ElwinBoots/Teensy_DualMotorBoard_V1/Firmware/MotionProfile.h

#ifndef __MOTIONPROFILE2_H__
#define __MOTIONPROFILE2_H__

class MotionProfile{		
public:	
	MotionProfile(float tstart, float t1, float t2, float t3, float p, float v_max, float a_max, float j_max, float Ts);	 
	void init();
	double stateCalculation( int input_status);
	double p2p_get_b( double t );
	double qref, vref, aref, jref;

	long REFstatus; 
	bool REFidir;
	float v, v_max, a_max, j_max, tstart, t1, t2, t3, Ts, rdelay;
	double REFiref, REFqmem;
  double p;
	double t, REFt0, REFt1, REFt2, REFt3, REFt4, REFt5, REFt6, REFt7, reltim;
	double REFs0, REFs1, REFs2, REFs3, REFs4, REFs5, REFs6, REFs7;
	double REFv0, REFv1, REFv2, REFv3, REFv4, REFv5, REFv6, REFv7;
	double REFa0, REFa1, REFa2, REFa3, REFa4, REFa5, REFa6, REFa7;
	double REFdelta, REFgamma, REFjerk, REFxstrt, j, jd;
	
protected:

	
	

};
#endif
