ElwinBoots/Teensy_DualMotorBoard_V1/trace.h

enum type {
  TYPE_INT8,
  TYPE_UINT8,
  TYPE_INT16,
  TYPE_UINT16,
  TYPE_INT32,
  TYPE_UINT32,
  TYPE_INT64,
  TYPE_UINT64,
  TYPE_FLOAT32,
  TYPE_FLOAT64
};

typedef struct trace_t{ 
  const char* names[500]; 
  uint8_t  all_types[500]; 
  uint8_t* all_pointers[500]; 
  uint32_t  all_lengths[500]; 
  uint8_t*  pointers[50]; 
  uint32_t  lengths[50]; 
  uint32_t n_to_send;
  bool send_all;
} trace_t; 

trace_t trace = 
{ 
  {
	"motor.conf1.anglechoice",
	"motor.conf1.advancefactor",
	"motor.conf1.reversecommutation",
	"motor.conf1.maxDutyCycle",
	"motor.conf1.ridethewave",
	"motor.conf1.commutationoffset",
	"motor.conf1.adc2A",
	"motor.conf1.ss_gain",
	"motor.conf1.enccountperrev",
	"motor.conf1.enc2rad",
	"motor.conf1.I_max",
	"motor.conf1.T_max",
	"motor.conf1.Kp_iq",
	"motor.conf1.Kp_id",
	"motor.conf1.Ki_iq",
	"motor.conf1.Ki_id",
	"motor.conf1.lowpass_Vq_c",
	"motor.conf1.lowpass_Vd_c",
	"motor.conf1.max_edeltarad",
	"motor.conf1.N_pp",
	"motor.conf1.clipMethod",
	"motor.conf1.maxerror",
	"motor.conf1.Command",
	"motor.conf1.Ld",
	"motor.conf1.Lq",
	"motor.conf1.Lambda_m",
	"motor.conf1.Kp",
	"motor.conf1.Ki",
	"motor.conf1.Kd",
	"motor.conf1.lowpass_c",
	"motor.conf1.Kp_prep",
	"motor.conf1.Ki_prep",
	"motor.conf1.Kd_prep",
	"motor.conf1.lowpass_c_prep",
	"motor.conf1.enc_transmission",
	"motor.conf2.anglechoice",
	"motor.conf2.advancefactor",
	"motor.conf2.reversecommutation",
	"motor.conf2.maxDutyCycle",
	"motor.conf2.ridethewave",
	"motor.conf2.commutationoffset",
	"motor.conf2.adc2A",
	"motor.conf2.ss_gain",
	"motor.conf2.enccountperrev",
	"motor.conf2.enc2rad",
	"motor.conf2.I_max",
	"motor.conf2.T_max",
	"motor.conf2.Kp_iq",
	"motor.conf2.Kp_id",
	"motor.conf2.Ki_iq",
	"motor.conf2.Ki_id",
	"motor.conf2.lowpass_Vq_c",
	"motor.conf2.lowpass_Vd_c",
	"motor.conf2.max_edeltarad",
	"motor.conf2.N_pp",
	"motor.conf2.clipMethod",
	"motor.conf2.maxerror",
	"motor.conf2.Command",
	"motor.conf2.Ld",
	"motor.conf2.Lq",
	"motor.conf2.Lambda_m",
	"motor.conf2.Kp",
	"motor.conf2.Ki",
	"motor.conf2.Kd",
	"motor.conf2.lowpass_c",
	"motor.conf2.Kp_prep",
	"motor.conf2.Ki_prep",
	"motor.conf2.Kd_prep",
	"motor.conf2.lowpass_c_prep",
	"motor.conf2.enc_transmission",
	"motor.conf.Ts",
	"motor.conf.T",
	"motor.conf.Busadc2Vbus",
	"motor.conf.V_Bus",
	"motor.conf.Ndownsample",
	"motor.conf.NdownsamplePRBS",
	"motor.conf.ss_fstart",
	"motor.conf.ss_fstep",
	"motor.conf.ss_fend",
	"motor.conf.ss_n_aver",
	"motor.state.sens1",
	"motor.state.sens2",
	"motor.state.sens3",
	"motor.state.sens4",
	"motor.state.sens1_lp",
	"motor.state.sens2_lp",
	"motor.state.sens3_lp",
	"motor.state.sens4_lp",
	"motor.state.sens1_calib",
	"motor.state.sens2_calib",
	"motor.state.sens3_calib",
	"motor.state.sens4_calib",
	"motor.state.sensBus_lp",
	"motor.state.sensCalVal1",
	"motor.state.sensCalVal2",
	"motor.state.sensCalVal3",
	"motor.state.sensCalVal4",
	"motor.state.sensBus",
	"motor.state.sensBus2",
	"motor.state.n_senscalib",
	"motor.state.setupready",
	"motor.state.curtime",
	"motor.state.prevtime",
	"motor.state.overloadcounter",
	"motor.state.is_v7",
	"motor.state.firsterror",
	"motor.state.curloop",
	"motor.state.downsample",
	"motor.state.ss_phase",
	"motor.state.lfsr",
	"motor.state.noisebit",
	"motor.state.ss_f",
	"motor.state.ss_tstart",
	"motor.state.downsamplePRBS",
	"motor.state.encoderPos1",
	"motor.state.encoderPos2",
	"motor.state.IndexFound1",
	"motor.state.IndexFound2",
	"motor.state1.streambuffer",
	"motor.state1.curbuffer",
	"motor.state1.buffergain",
	"motor.state1.runstream",
	"motor.state1.T_FF_acc",
	"motor.state1.T_FF_vel",
	"motor.state1.i_vector_radpers_act",
	"motor.state1.BEMFa",
	"motor.state1.BEMFb",
	"motor.state1.Ialpha_prev",
	"motor.state1.Ibeta_prev",
	"motor.state1.Vq",
	"motor.state1.Vd",
	"motor.state1.Valpha",
	"motor.state1.Vbeta",
	"motor.state1.thetawave",
	"motor.state1.Id_meas",
	"motor.state1.Iq_meas",
	"motor.state1.Id_meas_lp",
	"motor.state1.Iq_meas_lp",
	"motor.state1.Va",
	"motor.state1.Vb",
	"motor.state1.Vc",
	"motor.state1.VSP",
	"motor.state1.i_vector_radpers",
	"motor.state1.i_vector_acc",
	"motor.state1.Kp_out",
	"motor.state1.Kp_out_prev",
	"motor.state1.Kd_out",
	"motor.state1.Ki_sum",
	"motor.state1.Ki_out",
	"motor.state1.lp_out",
	"motor.state1.biquadout",
	"motor.state1.mechcontout",
	"motor.state1.Iout",
	"motor.state1.muziek_gain",
	"motor.state1.muziek_gain_V",
	"motor.state1.downsample",
	"motor.state1.REFstatus",
	"motor.state1.incomingByte",
	"motor.state1.encoderPos1",
	"motor.state1.encoderPos2",
	"motor.state1.IndexFound1",
	"motor.state1.IndexFound2",
	"motor.state1.OutputOn",
	"motor.state1.ss_out",
	"motor.state1.distoff",
	"motor.state1.dist",
	"motor.state1.distval",
	"motor.state1.SP_input_status",
	"motor.state1.spGO",
	"motor.state1.Jload",
	"motor.state1.velFF",
	"motor.state1.R",
	"motor.state1.offsetVelTot",
	"motor.state1.offsetVel",
	"motor.state1.offsetVel_lp",
	"motor.state1.offsetVel_lp_prev",
	"motor.state1.jerk",
	"motor.state1.acc",
	"motor.state1.vel",
	"motor.state1.Ialpha",
	"motor.state1.Ibeta",
	"motor.state1.thetaPark",
	"motor.state1.thetaParkPrev",
	"motor.state1.edeltarad",
	"motor.state1.eradpers_lp",
	"motor.state1.erpm",
	"motor.state1.thetaPark_enc",
	"motor.state1.thetaPark_obs",
	"motor.state1.thetaPark_obs_prev",
	"motor.state1.co",
	"motor.state1.si",
	"motor.state1.tA",
	"motor.state1.tB",
	"motor.state1.tC",
	"motor.state1.Id_e",
	"motor.state1.Id_SP",
	"motor.state1.Iq_e",
	"motor.state1.Iq_SP",
	"motor.state1.ia",
	"motor.state1.ib",
	"motor.state1.ic",
	"motor.state1.Vq_distgain",
	"motor.state1.Vd_distgain",
	"motor.state1.Iq_distgain",
	"motor.state1.Id_distgain",
	"motor.state1.mechdistgain",
	"motor.state1.rdistgain",
	"motor.state1.maxVolt",
	"motor.state1.Vtot",
	"motor.state1.rmech",
	"motor.state1.rdelay",
	"motor.state1.emech",
	"motor.state1.ymech",
	"motor.state1.rmechoffset",
	"motor.state1.we",
	"motor.state1.VqFF",
	"motor.state1.VdFF",
	"motor.state1.Iq_offset_SP",
	"motor.state1.Id_offset_SP",
	"motor.state1.Valpha_offset",
	"motor.state1.Vbeta_offset",
	"motor.state1.vq_int_state",
	"motor.state1.vd_int_state",
	"motor.state1.I_bus",
	"motor.state1.P_tot",
	"motor.state1.Kp_iq_out",
	"motor.state1.Ki_iq_out",
	"motor.state1.Kp_id_out",
	"motor.state1.Ki_id_out",
	"motor.state1.Vq_lp_out",
	"motor.state1.Vd_lp_out",
	"motor.state1.Vq_biquadout",
	"motor.state1.Vd_biquadout",
	"motor.state1.SPdir",
	"motor.state1.spNgo",
	"motor.state1.hfi_on",
	"motor.state1.hfi_V",
	"motor.state1.hfi_V_act",
	"motor.state1.hfi_dir",
	"motor.state1.hfi_dir_int",
	"motor.state1.hfi_gain",
	"motor.state1.hfi_curangleest",
	"motor.state1.hfi_gain_int2",
	"motor.state1.hfi_Id_meas_low",
	"motor.state1.hfi_Iq_meas_low",
	"motor.state1.hfi_Id_meas_high",
	"motor.state1.hfi_Iq_meas_high",
	"motor.state1.delta_id",
	"motor.state1.delta_iq",
	"motor.state1.hfi_firstcycle",
	"motor.state1.hfi_abs_pos",
	"motor.state1.hfi_useforfeedback",
	"motor.state1.hfi_use_lowpass",
	"motor.state1.hfi_prev",
	"motor.state1.hfi_distgain",
	"motor.state1.hfi_contout",
	"motor.state1.hfi_error",
	"motor.state1.hfi_method",
	"motor.state1.hfi_ffw",
	"motor.state1.hfi_maxvel",
	"motor.state1.diq_compensation",
	"motor.state1.diq_compensation_on",
	"motor.state1.compensation",
	"motor.state1.firsterror",
	"motor.state2.streambuffer",
	"motor.state2.curbuffer",
	"motor.state2.buffergain",
	"motor.state2.runstream",
	"motor.state2.T_FF_acc",
	"motor.state2.T_FF_vel",
	"motor.state2.i_vector_radpers_act",
	"motor.state2.BEMFa",
	"motor.state2.BEMFb",
	"motor.state2.Ialpha_prev",
	"motor.state2.Ibeta_prev",
	"motor.state2.Vq",
	"motor.state2.Vd",
	"motor.state2.Valpha",
	"motor.state2.Vbeta",
	"motor.state2.thetawave",
	"motor.state2.Id_meas",
	"motor.state2.Iq_meas",
	"motor.state2.Id_meas_lp",
	"motor.state2.Iq_meas_lp",
	"motor.state2.Va",
	"motor.state2.Vb",
	"motor.state2.Vc",
	"motor.state2.VSP",
	"motor.state2.i_vector_radpers",
	"motor.state2.i_vector_acc",
	"motor.state2.Kp_out",
	"motor.state2.Kp_out_prev",
	"motor.state2.Kd_out",
	"motor.state2.Ki_sum",
	"motor.state2.Ki_out",
	"motor.state2.lp_out",
	"motor.state2.biquadout",
	"motor.state2.mechcontout",
	"motor.state2.Iout",
	"motor.state2.muziek_gain",
	"motor.state2.muziek_gain_V",
	"motor.state2.downsample",
	"motor.state2.REFstatus",
	"motor.state2.incomingByte",
	"motor.state2.encoderPos1",
	"motor.state2.encoderPos2",
	"motor.state2.IndexFound1",
	"motor.state2.IndexFound2",
	"motor.state2.OutputOn",
	"motor.state2.ss_out",
	"motor.state2.distoff",
	"motor.state2.dist",
	"motor.state2.distval",
	"motor.state2.SP_input_status",
	"motor.state2.spGO",
	"motor.state2.Jload",
	"motor.state2.velFF",
	"motor.state2.R",
	"motor.state2.offsetVelTot",
	"motor.state2.offsetVel",
	"motor.state2.offsetVel_lp",
	"motor.state2.offsetVel_lp_prev",
	"motor.state2.jerk",
	"motor.state2.acc",
	"motor.state2.vel",
	"motor.state2.Ialpha",
	"motor.state2.Ibeta",
	"motor.state2.thetaPark",
	"motor.state2.thetaParkPrev",
	"motor.state2.edeltarad",
	"motor.state2.eradpers_lp",
	"motor.state2.erpm",
	"motor.state2.thetaPark_enc",
	"motor.state2.thetaPark_obs",
	"motor.state2.thetaPark_obs_prev",
	"motor.state2.co",
	"motor.state2.si",
	"motor.state2.tA",
	"motor.state2.tB",
	"motor.state2.tC",
	"motor.state2.Id_e",
	"motor.state2.Id_SP",
	"motor.state2.Iq_e",
	"motor.state2.Iq_SP",
	"motor.state2.ia",
	"motor.state2.ib",
	"motor.state2.ic",
	"motor.state2.Vq_distgain",
	"motor.state2.Vd_distgain",
	"motor.state2.Iq_distgain",
	"motor.state2.Id_distgain",
	"motor.state2.mechdistgain",
	"motor.state2.rdistgain",
	"motor.state2.maxVolt",
	"motor.state2.Vtot",
	"motor.state2.rmech",
	"motor.state2.rdelay",
	"motor.state2.emech",
	"motor.state2.ymech",
	"motor.state2.rmechoffset",
	"motor.state2.we",
	"motor.state2.VqFF",
	"motor.state2.VdFF",
	"motor.state2.Iq_offset_SP",
	"motor.state2.Id_offset_SP",
	"motor.state2.Valpha_offset",
	"motor.state2.Vbeta_offset",
	"motor.state2.vq_int_state",
	"motor.state2.vd_int_state",
	"motor.state2.I_bus",
	"motor.state2.P_tot",
	"motor.state2.Kp_iq_out",
	"motor.state2.Ki_iq_out",
	"motor.state2.Kp_id_out",
	"motor.state2.Ki_id_out",
	"motor.state2.Vq_lp_out",
	"motor.state2.Vd_lp_out",
	"motor.state2.Vq_biquadout",
	"motor.state2.Vd_biquadout",
	"motor.state2.SPdir",
	"motor.state2.spNgo",
	"motor.state2.hfi_on",
	"motor.state2.hfi_V",
	"motor.state2.hfi_V_act",
	"motor.state2.hfi_dir",
	"motor.state2.hfi_dir_int",
	"motor.state2.hfi_gain",
	"motor.state2.hfi_curangleest",
	"motor.state2.hfi_gain_int2",
	"motor.state2.hfi_Id_meas_low",
	"motor.state2.hfi_Iq_meas_low",
	"motor.state2.hfi_Id_meas_high",
	"motor.state2.hfi_Iq_meas_high",
	"motor.state2.delta_id",
	"motor.state2.delta_iq",
	"motor.state2.hfi_firstcycle",
	"motor.state2.hfi_abs_pos",
	"motor.state2.hfi_useforfeedback",
	"motor.state2.hfi_use_lowpass",
	"motor.state2.hfi_prev",
	"motor.state2.hfi_distgain",
	"motor.state2.hfi_contout",
	"motor.state2.hfi_error",
	"motor.state2.hfi_method",
	"motor.state2.hfi_ffw",
	"motor.state2.hfi_maxvel",
	"motor.state2.diq_compensation",
	"motor.state2.diq_compensation_on",
	"motor.state2.compensation",
	"motor.state2.firsterror",
  }
,
  {
	 TYPE_INT32,
	 TYPE_FLOAT32,
	 TYPE_INT8,
	 TYPE_FLOAT32,
	 TYPE_UINT32,
	 TYPE_FLOAT32,
	 TYPE_FLOAT32,
	 TYPE_FLOAT32,
	 TYPE_INT32,
	 TYPE_FLOAT64,
	 TYPE_FLOAT32,
	 TYPE_FLOAT32,
	 TYPE_FLOAT32,
	 TYPE_FLOAT32,
	 TYPE_FLOAT32,
	 TYPE_FLOAT32,
	 TYPE_FLOAT32,
	 TYPE_FLOAT32,
	 TYPE_FLOAT32,
	 TYPE_FLOAT32,
	 TYPE_UINT32,
	 TYPE_FLOAT32,
	 TYPE_UINT32,
	 TYPE_FLOAT32,
	 TYPE_FLOAT32,
	 TYPE_FLOAT32,
	 TYPE_FLOAT32,
	 TYPE_FLOAT32,
	 TYPE_FLOAT32,
	 TYPE_FLOAT32,
	 TYPE_FLOAT32,
	 TYPE_FLOAT32,
	 TYPE_FLOAT32,
	 TYPE_FLOAT32,
	 TYPE_FLOAT32,
	 TYPE_INT32,
	 TYPE_FLOAT32,
	 TYPE_INT8,
	 TYPE_FLOAT32,
	 TYPE_UINT32,
	 TYPE_FLOAT32,
	 TYPE_FLOAT32,
	 TYPE_FLOAT32,
	 TYPE_INT32,
	 TYPE_FLOAT64,
	 TYPE_FLOAT32,
	 TYPE_FLOAT32,
	 TYPE_FLOAT32,
	 TYPE_FLOAT32,
	 TYPE_FLOAT32,
	 TYPE_FLOAT32,
	 TYPE_FLOAT32,
	 TYPE_FLOAT32,
	 TYPE_FLOAT32,
	 TYPE_FLOAT32,
	 TYPE_UINT32,
	 TYPE_FLOAT32,
	 TYPE_UINT32,
	 TYPE_FLOAT32,
	 TYPE_FLOAT32,
	 TYPE_FLOAT32,
	 TYPE_FLOAT32,
	 TYPE_FLOAT32,
	 TYPE_FLOAT32,
	 TYPE_FLOAT32,
	 TYPE_FLOAT32,
	 TYPE_FLOAT32,
	 TYPE_FLOAT32,
	 TYPE_FLOAT32,
	 TYPE_FLOAT32,
	 TYPE_FLOAT32,
	 TYPE_FLOAT32,
	 TYPE_FLOAT32,
	 TYPE_FLOAT32,
	 TYPE_UINT32,
	 TYPE_UINT32,
	 TYPE_FLOAT32,
	 TYPE_FLOAT32,
	 TYPE_FLOAT32,
	 TYPE_UINT32,
	 TYPE_FLOAT32,
	 TYPE_FLOAT32,
	 TYPE_FLOAT32,
	 TYPE_FLOAT32,
	 TYPE_FLOAT32,
	 TYPE_FLOAT32,
	 TYPE_FLOAT32,
	 TYPE_FLOAT32,
	 TYPE_FLOAT32,
	 TYPE_FLOAT32,
	 TYPE_FLOAT32,
	 TYPE_FLOAT32,
	 TYPE_FLOAT32,
	 TYPE_FLOAT32,
	 TYPE_FLOAT32,
	 TYPE_FLOAT32,
	 TYPE_FLOAT32,
	 TYPE_FLOAT32,
	 TYPE_FLOAT32,
	 TYPE_INT32,
	 TYPE_INT8,
	 TYPE_UINT32,
	 TYPE_UINT32,
	 TYPE_UINT32,
	 TYPE_INT8,
	 TYPE_UINT32,
	 TYPE_UINT32,
	 TYPE_UINT32,
	 TYPE_FLOAT32,
	 TYPE_UINT16,
	 TYPE_UINT16,
	 TYPE_FLOAT32,
	 TYPE_FLOAT32,
	 TYPE_UINT32,
	 TYPE_INT32,
	 TYPE_INT32,
	 TYPE_UINT32,
	 TYPE_UINT32,
	 TYPE_FLOAT32,
	 TYPE_UINT32,
	 TYPE_FLOAT32,
	 TYPE_INT8,
	 TYPE_FLOAT32,
	 TYPE_FLOAT32,
	 TYPE_FLOAT32,
	 TYPE_FLOAT32,
	 TYPE_FLOAT32,
	 TYPE_FLOAT32,
	 TYPE_FLOAT32,
	 TYPE_FLOAT32,
	 TYPE_FLOAT32,
	 TYPE_FLOAT32,
	 TYPE_FLOAT32,
	 TYPE_FLOAT32,
	 TYPE_FLOAT32,
	 TYPE_FLOAT32,
	 TYPE_FLOAT32,
	 TYPE_FLOAT32,
	 TYPE_FLOAT32,
	 TYPE_FLOAT32,
	 TYPE_FLOAT32,
	 TYPE_FLOAT32,
	 TYPE_FLOAT32,
	 TYPE_FLOAT32,
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
	(uint8_t*)&motor.conf1.advancefactor,
	(uint8_t*)&motor.conf1.reversecommutation,
	(uint8_t*)&motor.conf1.maxDutyCycle,
	(uint8_t*)&motor.conf1.ridethewave,
	(uint8_t*)&motor.conf1.commutationoffset,
	(uint8_t*)&motor.conf1.adc2A,
	(uint8_t*)&motor.conf1.ss_gain,
	(uint8_t*)&motor.conf1.enccountperrev,
	(uint8_t*)&motor.conf1.enc2rad,
	(uint8_t*)&motor.conf1.I_max,
	(uint8_t*)&motor.conf1.T_max,
	(uint8_t*)&motor.conf1.Kp_iq,
	(uint8_t*)&motor.conf1.Kp_id,
	(uint8_t*)&motor.conf1.Ki_iq,
	(uint8_t*)&motor.conf1.Ki_id,
	(uint8_t*)&motor.conf1.lowpass_Vq_c,
	(uint8_t*)&motor.conf1.lowpass_Vd_c,
	(uint8_t*)&motor.conf1.max_edeltarad,
	(uint8_t*)&motor.conf1.N_pp,
	(uint8_t*)&motor.conf1.clipMethod,
	(uint8_t*)&motor.conf1.maxerror,
	(uint8_t*)&motor.conf1.Command,
	(uint8_t*)&motor.conf1.Ld,
	(uint8_t*)&motor.conf1.Lq,
	(uint8_t*)&motor.conf1.Lambda_m,
	(uint8_t*)&motor.conf1.Kp,
	(uint8_t*)&motor.conf1.Ki,
	(uint8_t*)&motor.conf1.Kd,
	(uint8_t*)&motor.conf1.lowpass_c,
	(uint8_t*)&motor.conf1.Kp_prep,
	(uint8_t*)&motor.conf1.Ki_prep,
	(uint8_t*)&motor.conf1.Kd_prep,
	(uint8_t*)&motor.conf1.lowpass_c_prep,
	(uint8_t*)&motor.conf1.enc_transmission,
	(uint8_t*)&motor.conf2.anglechoice,
	(uint8_t*)&motor.conf2.advancefactor,
	(uint8_t*)&motor.conf2.reversecommutation,
	(uint8_t*)&motor.conf2.maxDutyCycle,
	(uint8_t*)&motor.conf2.ridethewave,
	(uint8_t*)&motor.conf2.commutationoffset,
	(uint8_t*)&motor.conf2.adc2A,
	(uint8_t*)&motor.conf2.ss_gain,
	(uint8_t*)&motor.conf2.enccountperrev,
	(uint8_t*)&motor.conf2.enc2rad,
	(uint8_t*)&motor.conf2.I_max,
	(uint8_t*)&motor.conf2.T_max,
	(uint8_t*)&motor.conf2.Kp_iq,
	(uint8_t*)&motor.conf2.Kp_id,
	(uint8_t*)&motor.conf2.Ki_iq,
	(uint8_t*)&motor.conf2.Ki_id,
	(uint8_t*)&motor.conf2.lowpass_Vq_c,
	(uint8_t*)&motor.conf2.lowpass_Vd_c,
	(uint8_t*)&motor.conf2.max_edeltarad,
	(uint8_t*)&motor.conf2.N_pp,
	(uint8_t*)&motor.conf2.clipMethod,
	(uint8_t*)&motor.conf2.maxerror,
	(uint8_t*)&motor.conf2.Command,
	(uint8_t*)&motor.conf2.Ld,
	(uint8_t*)&motor.conf2.Lq,
	(uint8_t*)&motor.conf2.Lambda_m,
	(uint8_t*)&motor.conf2.Kp,
	(uint8_t*)&motor.conf2.Ki,
	(uint8_t*)&motor.conf2.Kd,
	(uint8_t*)&motor.conf2.lowpass_c,
	(uint8_t*)&motor.conf2.Kp_prep,
	(uint8_t*)&motor.conf2.Ki_prep,
	(uint8_t*)&motor.conf2.Kd_prep,
	(uint8_t*)&motor.conf2.lowpass_c_prep,
	(uint8_t*)&motor.conf2.enc_transmission,
	(uint8_t*)&motor.conf.Ts,
	(uint8_t*)&motor.conf.T,
	(uint8_t*)&motor.conf.Busadc2Vbus,
	(uint8_t*)&motor.conf.V_Bus,
	(uint8_t*)&motor.conf.Ndownsample,
	(uint8_t*)&motor.conf.NdownsamplePRBS,
	(uint8_t*)&motor.conf.ss_fstart,
	(uint8_t*)&motor.conf.ss_fstep,
	(uint8_t*)&motor.conf.ss_fend,
	(uint8_t*)&motor.conf.ss_n_aver,
	(uint8_t*)&motor.state.sens1,
	(uint8_t*)&motor.state.sens2,
	(uint8_t*)&motor.state.sens3,
	(uint8_t*)&motor.state.sens4,
	(uint8_t*)&motor.state.sens1_lp,
	(uint8_t*)&motor.state.sens2_lp,
	(uint8_t*)&motor.state.sens3_lp,
	(uint8_t*)&motor.state.sens4_lp,
	(uint8_t*)&motor.state.sens1_calib,
	(uint8_t*)&motor.state.sens2_calib,
	(uint8_t*)&motor.state.sens3_calib,
	(uint8_t*)&motor.state.sens4_calib,
	(uint8_t*)&motor.state.sensBus_lp,
	(uint8_t*)&motor.state.sensCalVal1,
	(uint8_t*)&motor.state.sensCalVal2,
	(uint8_t*)&motor.state.sensCalVal3,
	(uint8_t*)&motor.state.sensCalVal4,
	(uint8_t*)&motor.state.sensBus,
	(uint8_t*)&motor.state.sensBus2,
	(uint8_t*)&motor.state.n_senscalib,
	(uint8_t*)&motor.state.setupready,
	(uint8_t*)&motor.state.curtime,
	(uint8_t*)&motor.state.prevtime,
	(uint8_t*)&motor.state.overloadcounter,
	(uint8_t*)&motor.state.is_v7,
	(uint8_t*)&motor.state.firsterror,
	(uint8_t*)&motor.state.curloop,
	(uint8_t*)&motor.state.downsample,
	(uint8_t*)&motor.state.ss_phase,
	(uint8_t*)&motor.state.lfsr,
	(uint8_t*)&motor.state.noisebit,
	(uint8_t*)&motor.state.ss_f,
	(uint8_t*)&motor.state.ss_tstart,
	(uint8_t*)&motor.state.downsamplePRBS,
	(uint8_t*)&motor.state.encoderPos1,
	(uint8_t*)&motor.state.encoderPos2,
	(uint8_t*)&motor.state.IndexFound1,
	(uint8_t*)&motor.state.IndexFound2,
	(uint8_t*)&motor.state1.streambuffer,
	(uint8_t*)&motor.state1.curbuffer,
	(uint8_t*)&motor.state1.buffergain,
	(uint8_t*)&motor.state1.runstream,
	(uint8_t*)&motor.state1.T_FF_acc,
	(uint8_t*)&motor.state1.T_FF_vel,
	(uint8_t*)&motor.state1.i_vector_radpers_act,
	(uint8_t*)&motor.state1.BEMFa,
	(uint8_t*)&motor.state1.BEMFb,
	(uint8_t*)&motor.state1.Ialpha_prev,
	(uint8_t*)&motor.state1.Ibeta_prev,
	(uint8_t*)&motor.state1.Vq,
	(uint8_t*)&motor.state1.Vd,
	(uint8_t*)&motor.state1.Valpha,
	(uint8_t*)&motor.state1.Vbeta,
	(uint8_t*)&motor.state1.thetawave,
	(uint8_t*)&motor.state1.Id_meas,
	(uint8_t*)&motor.state1.Iq_meas,
	(uint8_t*)&motor.state1.Id_meas_lp,
	(uint8_t*)&motor.state1.Iq_meas_lp,
	(uint8_t*)&motor.state1.Va,
	(uint8_t*)&motor.state1.Vb,
	(uint8_t*)&motor.state1.Vc,
	(uint8_t*)&motor.state1.VSP,
	(uint8_t*)&motor.state1.i_vector_radpers,
	(uint8_t*)&motor.state1.i_vector_acc,
	(uint8_t*)&motor.state1.Kp_out,
	(uint8_t*)&motor.state1.Kp_out_prev,
	(uint8_t*)&motor.state1.Kd_out,
	(uint8_t*)&motor.state1.Ki_sum,
	(uint8_t*)&motor.state1.Ki_out,
	(uint8_t*)&motor.state1.lp_out,
	(uint8_t*)&motor.state1.biquadout,
	(uint8_t*)&motor.state1.mechcontout,
	(uint8_t*)&motor.state1.Iout,
	(uint8_t*)&motor.state1.muziek_gain,
	(uint8_t*)&motor.state1.muziek_gain_V,
	(uint8_t*)&motor.state1.downsample,
	(uint8_t*)&motor.state1.REFstatus,
	(uint8_t*)&motor.state1.incomingByte,
	(uint8_t*)&motor.state1.encoderPos1,
	(uint8_t*)&motor.state1.encoderPos2,
	(uint8_t*)&motor.state1.IndexFound1,
	(uint8_t*)&motor.state1.IndexFound2,
	(uint8_t*)&motor.state1.OutputOn,
	(uint8_t*)&motor.state1.ss_out,
	(uint8_t*)&motor.state1.distoff,
	(uint8_t*)&motor.state1.dist,
	(uint8_t*)&motor.state1.distval,
	(uint8_t*)&motor.state1.SP_input_status,
	(uint8_t*)&motor.state1.spGO,
	(uint8_t*)&motor.state1.Jload,
	(uint8_t*)&motor.state1.velFF,
	(uint8_t*)&motor.state1.R,
	(uint8_t*)&motor.state1.offsetVelTot,
	(uint8_t*)&motor.state1.offsetVel,
	(uint8_t*)&motor.state1.offsetVel_lp,
	(uint8_t*)&motor.state1.offsetVel_lp_prev,
	(uint8_t*)&motor.state1.jerk,
	(uint8_t*)&motor.state1.acc,
	(uint8_t*)&motor.state1.vel,
	(uint8_t*)&motor.state1.Ialpha,
	(uint8_t*)&motor.state1.Ibeta,
	(uint8_t*)&motor.state1.thetaPark,
	(uint8_t*)&motor.state1.thetaParkPrev,
	(uint8_t*)&motor.state1.edeltarad,
	(uint8_t*)&motor.state1.eradpers_lp,
	(uint8_t*)&motor.state1.erpm,
	(uint8_t*)&motor.state1.thetaPark_enc,
	(uint8_t*)&motor.state1.thetaPark_obs,
	(uint8_t*)&motor.state1.thetaPark_obs_prev,
	(uint8_t*)&motor.state1.co,
	(uint8_t*)&motor.state1.si,
	(uint8_t*)&motor.state1.tA,
	(uint8_t*)&motor.state1.tB,
	(uint8_t*)&motor.state1.tC,
	(uint8_t*)&motor.state1.Id_e,
	(uint8_t*)&motor.state1.Id_SP,
	(uint8_t*)&motor.state1.Iq_e,
	(uint8_t*)&motor.state1.Iq_SP,
	(uint8_t*)&motor.state1.ia,
	(uint8_t*)&motor.state1.ib,
	(uint8_t*)&motor.state1.ic,
	(uint8_t*)&motor.state1.Vq_distgain,
	(uint8_t*)&motor.state1.Vd_distgain,
	(uint8_t*)&motor.state1.Iq_distgain,
	(uint8_t*)&motor.state1.Id_distgain,
	(uint8_t*)&motor.state1.mechdistgain,
	(uint8_t*)&motor.state1.rdistgain,
	(uint8_t*)&motor.state1.maxVolt,
	(uint8_t*)&motor.state1.Vtot,
	(uint8_t*)&motor.state1.rmech,
	(uint8_t*)&motor.state1.rdelay,
	(uint8_t*)&motor.state1.emech,
	(uint8_t*)&motor.state1.ymech,
	(uint8_t*)&motor.state1.rmechoffset,
	(uint8_t*)&motor.state1.we,
	(uint8_t*)&motor.state1.VqFF,
	(uint8_t*)&motor.state1.VdFF,
	(uint8_t*)&motor.state1.Iq_offset_SP,
	(uint8_t*)&motor.state1.Id_offset_SP,
	(uint8_t*)&motor.state1.Valpha_offset,
	(uint8_t*)&motor.state1.Vbeta_offset,
	(uint8_t*)&motor.state1.vq_int_state,
	(uint8_t*)&motor.state1.vd_int_state,
	(uint8_t*)&motor.state1.I_bus,
	(uint8_t*)&motor.state1.P_tot,
	(uint8_t*)&motor.state1.Kp_iq_out,
	(uint8_t*)&motor.state1.Ki_iq_out,
	(uint8_t*)&motor.state1.Kp_id_out,
	(uint8_t*)&motor.state1.Ki_id_out,
	(uint8_t*)&motor.state1.Vq_lp_out,
	(uint8_t*)&motor.state1.Vd_lp_out,
	(uint8_t*)&motor.state1.Vq_biquadout,
	(uint8_t*)&motor.state1.Vd_biquadout,
	(uint8_t*)&motor.state1.SPdir,
	(uint8_t*)&motor.state1.spNgo,
	(uint8_t*)&motor.state1.hfi_on,
	(uint8_t*)&motor.state1.hfi_V,
	(uint8_t*)&motor.state1.hfi_V_act,
	(uint8_t*)&motor.state1.hfi_dir,
	(uint8_t*)&motor.state1.hfi_dir_int,
	(uint8_t*)&motor.state1.hfi_gain,
	(uint8_t*)&motor.state1.hfi_curangleest,
	(uint8_t*)&motor.state1.hfi_gain_int2,
	(uint8_t*)&motor.state1.hfi_Id_meas_low,
	(uint8_t*)&motor.state1.hfi_Iq_meas_low,
	(uint8_t*)&motor.state1.hfi_Id_meas_high,
	(uint8_t*)&motor.state1.hfi_Iq_meas_high,
	(uint8_t*)&motor.state1.delta_id,
	(uint8_t*)&motor.state1.delta_iq,
	(uint8_t*)&motor.state1.hfi_firstcycle,
	(uint8_t*)&motor.state1.hfi_abs_pos,
	(uint8_t*)&motor.state1.hfi_useforfeedback,
	(uint8_t*)&motor.state1.hfi_use_lowpass,
	(uint8_t*)&motor.state1.hfi_prev,
	(uint8_t*)&motor.state1.hfi_distgain,
	(uint8_t*)&motor.state1.hfi_contout,
	(uint8_t*)&motor.state1.hfi_error,
	(uint8_t*)&motor.state1.hfi_method,
	(uint8_t*)&motor.state1.hfi_ffw,
	(uint8_t*)&motor.state1.hfi_maxvel,
	(uint8_t*)&motor.state1.diq_compensation,
	(uint8_t*)&motor.state1.diq_compensation_on,
	(uint8_t*)&motor.state1.compensation,
	(uint8_t*)&motor.state1.firsterror,
	(uint8_t*)&motor.state2.streambuffer,
	(uint8_t*)&motor.state2.curbuffer,
	(uint8_t*)&motor.state2.buffergain,
	(uint8_t*)&motor.state2.runstream,
	(uint8_t*)&motor.state2.T_FF_acc,
	(uint8_t*)&motor.state2.T_FF_vel,
	(uint8_t*)&motor.state2.i_vector_radpers_act,
	(uint8_t*)&motor.state2.BEMFa,
	(uint8_t*)&motor.state2.BEMFb,
	(uint8_t*)&motor.state2.Ialpha_prev,
	(uint8_t*)&motor.state2.Ibeta_prev,
	(uint8_t*)&motor.state2.Vq,
	(uint8_t*)&motor.state2.Vd,
	(uint8_t*)&motor.state2.Valpha,
	(uint8_t*)&motor.state2.Vbeta,
	(uint8_t*)&motor.state2.thetawave,
	(uint8_t*)&motor.state2.Id_meas,
	(uint8_t*)&motor.state2.Iq_meas,
	(uint8_t*)&motor.state2.Id_meas_lp,
	(uint8_t*)&motor.state2.Iq_meas_lp,
	(uint8_t*)&motor.state2.Va,
	(uint8_t*)&motor.state2.Vb,
	(uint8_t*)&motor.state2.Vc,
	(uint8_t*)&motor.state2.VSP,
	(uint8_t*)&motor.state2.i_vector_radpers,
	(uint8_t*)&motor.state2.i_vector_acc,
	(uint8_t*)&motor.state2.Kp_out,
	(uint8_t*)&motor.state2.Kp_out_prev,
	(uint8_t*)&motor.state2.Kd_out,
	(uint8_t*)&motor.state2.Ki_sum,
	(uint8_t*)&motor.state2.Ki_out,
	(uint8_t*)&motor.state2.lp_out,
	(uint8_t*)&motor.state2.biquadout,
	(uint8_t*)&motor.state2.mechcontout,
	(uint8_t*)&motor.state2.Iout,
	(uint8_t*)&motor.state2.muziek_gain,
	(uint8_t*)&motor.state2.muziek_gain_V,
	(uint8_t*)&motor.state2.downsample,
	(uint8_t*)&motor.state2.REFstatus,
	(uint8_t*)&motor.state2.incomingByte,
	(uint8_t*)&motor.state2.encoderPos1,
	(uint8_t*)&motor.state2.encoderPos2,
	(uint8_t*)&motor.state2.IndexFound1,
	(uint8_t*)&motor.state2.IndexFound2,
	(uint8_t*)&motor.state2.OutputOn,
	(uint8_t*)&motor.state2.ss_out,
	(uint8_t*)&motor.state2.distoff,
	(uint8_t*)&motor.state2.dist,
	(uint8_t*)&motor.state2.distval,
	(uint8_t*)&motor.state2.SP_input_status,
	(uint8_t*)&motor.state2.spGO,
	(uint8_t*)&motor.state2.Jload,
	(uint8_t*)&motor.state2.velFF,
	(uint8_t*)&motor.state2.R,
	(uint8_t*)&motor.state2.offsetVelTot,
	(uint8_t*)&motor.state2.offsetVel,
	(uint8_t*)&motor.state2.offsetVel_lp,
	(uint8_t*)&motor.state2.offsetVel_lp_prev,
	(uint8_t*)&motor.state2.jerk,
	(uint8_t*)&motor.state2.acc,
	(uint8_t*)&motor.state2.vel,
	(uint8_t*)&motor.state2.Ialpha,
	(uint8_t*)&motor.state2.Ibeta,
	(uint8_t*)&motor.state2.thetaPark,
	(uint8_t*)&motor.state2.thetaParkPrev,
	(uint8_t*)&motor.state2.edeltarad,
	(uint8_t*)&motor.state2.eradpers_lp,
	(uint8_t*)&motor.state2.erpm,
	(uint8_t*)&motor.state2.thetaPark_enc,
	(uint8_t*)&motor.state2.thetaPark_obs,
	(uint8_t*)&motor.state2.thetaPark_obs_prev,
	(uint8_t*)&motor.state2.co,
	(uint8_t*)&motor.state2.si,
	(uint8_t*)&motor.state2.tA,
	(uint8_t*)&motor.state2.tB,
	(uint8_t*)&motor.state2.tC,
	(uint8_t*)&motor.state2.Id_e,
	(uint8_t*)&motor.state2.Id_SP,
	(uint8_t*)&motor.state2.Iq_e,
	(uint8_t*)&motor.state2.Iq_SP,
	(uint8_t*)&motor.state2.ia,
	(uint8_t*)&motor.state2.ib,
	(uint8_t*)&motor.state2.ic,
	(uint8_t*)&motor.state2.Vq_distgain,
	(uint8_t*)&motor.state2.Vd_distgain,
	(uint8_t*)&motor.state2.Iq_distgain,
	(uint8_t*)&motor.state2.Id_distgain,
	(uint8_t*)&motor.state2.mechdistgain,
	(uint8_t*)&motor.state2.rdistgain,
	(uint8_t*)&motor.state2.maxVolt,
	(uint8_t*)&motor.state2.Vtot,
	(uint8_t*)&motor.state2.rmech,
	(uint8_t*)&motor.state2.rdelay,
	(uint8_t*)&motor.state2.emech,
	(uint8_t*)&motor.state2.ymech,
	(uint8_t*)&motor.state2.rmechoffset,
	(uint8_t*)&motor.state2.we,
	(uint8_t*)&motor.state2.VqFF,
	(uint8_t*)&motor.state2.VdFF,
	(uint8_t*)&motor.state2.Iq_offset_SP,
	(uint8_t*)&motor.state2.Id_offset_SP,
	(uint8_t*)&motor.state2.Valpha_offset,
	(uint8_t*)&motor.state2.Vbeta_offset,
	(uint8_t*)&motor.state2.vq_int_state,
	(uint8_t*)&motor.state2.vd_int_state,
	(uint8_t*)&motor.state2.I_bus,
	(uint8_t*)&motor.state2.P_tot,
	(uint8_t*)&motor.state2.Kp_iq_out,
	(uint8_t*)&motor.state2.Ki_iq_out,
	(uint8_t*)&motor.state2.Kp_id_out,
	(uint8_t*)&motor.state2.Ki_id_out,
	(uint8_t*)&motor.state2.Vq_lp_out,
	(uint8_t*)&motor.state2.Vd_lp_out,
	(uint8_t*)&motor.state2.Vq_biquadout,
	(uint8_t*)&motor.state2.Vd_biquadout,
	(uint8_t*)&motor.state2.SPdir,
	(uint8_t*)&motor.state2.spNgo,
	(uint8_t*)&motor.state2.hfi_on,
	(uint8_t*)&motor.state2.hfi_V,
	(uint8_t*)&motor.state2.hfi_V_act,
	(uint8_t*)&motor.state2.hfi_dir,
	(uint8_t*)&motor.state2.hfi_dir_int,
	(uint8_t*)&motor.state2.hfi_gain,
	(uint8_t*)&motor.state2.hfi_curangleest,
	(uint8_t*)&motor.state2.hfi_gain_int2,
	(uint8_t*)&motor.state2.hfi_Id_meas_low,
	(uint8_t*)&motor.state2.hfi_Iq_meas_low,
	(uint8_t*)&motor.state2.hfi_Id_meas_high,
	(uint8_t*)&motor.state2.hfi_Iq_meas_high,
	(uint8_t*)&motor.state2.delta_id,
	(uint8_t*)&motor.state2.delta_iq,
	(uint8_t*)&motor.state2.hfi_firstcycle,
	(uint8_t*)&motor.state2.hfi_abs_pos,
	(uint8_t*)&motor.state2.hfi_useforfeedback,
	(uint8_t*)&motor.state2.hfi_use_lowpass,
	(uint8_t*)&motor.state2.hfi_prev,
	(uint8_t*)&motor.state2.hfi_distgain,
	(uint8_t*)&motor.state2.hfi_contout,
	(uint8_t*)&motor.state2.hfi_error,
	(uint8_t*)&motor.state2.hfi_method,
	(uint8_t*)&motor.state2.hfi_ffw,
	(uint8_t*)&motor.state2.hfi_maxvel,
	(uint8_t*)&motor.state2.diq_compensation,
	(uint8_t*)&motor.state2.diq_compensation_on,
	(uint8_t*)&motor.state2.compensation,
	(uint8_t*)&motor.state2.firsterror,
  }
,
  {
	sizeof(motor.conf1.anglechoice),
	sizeof(motor.conf1.advancefactor),
	sizeof(motor.conf1.reversecommutation),
	sizeof(motor.conf1.maxDutyCycle),
	sizeof(motor.conf1.ridethewave),
	sizeof(motor.conf1.commutationoffset),
	sizeof(motor.conf1.adc2A),
	sizeof(motor.conf1.ss_gain),
	sizeof(motor.conf1.enccountperrev),
	sizeof(motor.conf1.enc2rad),
	sizeof(motor.conf1.I_max),
	sizeof(motor.conf1.T_max),
	sizeof(motor.conf1.Kp_iq),
	sizeof(motor.conf1.Kp_id),
	sizeof(motor.conf1.Ki_iq),
	sizeof(motor.conf1.Ki_id),
	sizeof(motor.conf1.lowpass_Vq_c),
	sizeof(motor.conf1.lowpass_Vd_c),
	sizeof(motor.conf1.max_edeltarad),
	sizeof(motor.conf1.N_pp),
	sizeof(motor.conf1.clipMethod),
	sizeof(motor.conf1.maxerror),
	sizeof(motor.conf1.Command),
	sizeof(motor.conf1.Ld),
	sizeof(motor.conf1.Lq),
	sizeof(motor.conf1.Lambda_m),
	sizeof(motor.conf1.Kp),
	sizeof(motor.conf1.Ki),
	sizeof(motor.conf1.Kd),
	sizeof(motor.conf1.lowpass_c),
	sizeof(motor.conf1.Kp_prep),
	sizeof(motor.conf1.Ki_prep),
	sizeof(motor.conf1.Kd_prep),
	sizeof(motor.conf1.lowpass_c_prep),
	sizeof(motor.conf1.enc_transmission),
	sizeof(motor.conf2.anglechoice),
	sizeof(motor.conf2.advancefactor),
	sizeof(motor.conf2.reversecommutation),
	sizeof(motor.conf2.maxDutyCycle),
	sizeof(motor.conf2.ridethewave),
	sizeof(motor.conf2.commutationoffset),
	sizeof(motor.conf2.adc2A),
	sizeof(motor.conf2.ss_gain),
	sizeof(motor.conf2.enccountperrev),
	sizeof(motor.conf2.enc2rad),
	sizeof(motor.conf2.I_max),
	sizeof(motor.conf2.T_max),
	sizeof(motor.conf2.Kp_iq),
	sizeof(motor.conf2.Kp_id),
	sizeof(motor.conf2.Ki_iq),
	sizeof(motor.conf2.Ki_id),
	sizeof(motor.conf2.lowpass_Vq_c),
	sizeof(motor.conf2.lowpass_Vd_c),
	sizeof(motor.conf2.max_edeltarad),
	sizeof(motor.conf2.N_pp),
	sizeof(motor.conf2.clipMethod),
	sizeof(motor.conf2.maxerror),
	sizeof(motor.conf2.Command),
	sizeof(motor.conf2.Ld),
	sizeof(motor.conf2.Lq),
	sizeof(motor.conf2.Lambda_m),
	sizeof(motor.conf2.Kp),
	sizeof(motor.conf2.Ki),
	sizeof(motor.conf2.Kd),
	sizeof(motor.conf2.lowpass_c),
	sizeof(motor.conf2.Kp_prep),
	sizeof(motor.conf2.Ki_prep),
	sizeof(motor.conf2.Kd_prep),
	sizeof(motor.conf2.lowpass_c_prep),
	sizeof(motor.conf2.enc_transmission),
	sizeof(motor.conf.Ts),
	sizeof(motor.conf.T),
	sizeof(motor.conf.Busadc2Vbus),
	sizeof(motor.conf.V_Bus),
	sizeof(motor.conf.Ndownsample),
	sizeof(motor.conf.NdownsamplePRBS),
	sizeof(motor.conf.ss_fstart),
	sizeof(motor.conf.ss_fstep),
	sizeof(motor.conf.ss_fend),
	sizeof(motor.conf.ss_n_aver),
	sizeof(motor.state.sens1),
	sizeof(motor.state.sens2),
	sizeof(motor.state.sens3),
	sizeof(motor.state.sens4),
	sizeof(motor.state.sens1_lp),
	sizeof(motor.state.sens2_lp),
	sizeof(motor.state.sens3_lp),
	sizeof(motor.state.sens4_lp),
	sizeof(motor.state.sens1_calib),
	sizeof(motor.state.sens2_calib),
	sizeof(motor.state.sens3_calib),
	sizeof(motor.state.sens4_calib),
	sizeof(motor.state.sensBus_lp),
	sizeof(motor.state.sensCalVal1),
	sizeof(motor.state.sensCalVal2),
	sizeof(motor.state.sensCalVal3),
	sizeof(motor.state.sensCalVal4),
	sizeof(motor.state.sensBus),
	sizeof(motor.state.sensBus2),
	sizeof(motor.state.n_senscalib),
	sizeof(motor.state.setupready),
	sizeof(motor.state.curtime),
	sizeof(motor.state.prevtime),
	sizeof(motor.state.overloadcounter),
	sizeof(motor.state.is_v7),
	sizeof(motor.state.firsterror),
	sizeof(motor.state.curloop),
	sizeof(motor.state.downsample),
	sizeof(motor.state.ss_phase),
	sizeof(motor.state.lfsr),
	sizeof(motor.state.noisebit),
	sizeof(motor.state.ss_f),
	sizeof(motor.state.ss_tstart),
	sizeof(motor.state.downsamplePRBS),
	sizeof(motor.state.encoderPos1),
	sizeof(motor.state.encoderPos2),
	sizeof(motor.state.IndexFound1),
	sizeof(motor.state.IndexFound2),
	sizeof(motor.state1.streambuffer),
	sizeof(motor.state1.curbuffer),
	sizeof(motor.state1.buffergain),
	sizeof(motor.state1.runstream),
	sizeof(motor.state1.T_FF_acc),
	sizeof(motor.state1.T_FF_vel),
	sizeof(motor.state1.i_vector_radpers_act),
	sizeof(motor.state1.BEMFa),
	sizeof(motor.state1.BEMFb),
	sizeof(motor.state1.Ialpha_prev),
	sizeof(motor.state1.Ibeta_prev),
	sizeof(motor.state1.Vq),
	sizeof(motor.state1.Vd),
	sizeof(motor.state1.Valpha),
	sizeof(motor.state1.Vbeta),
	sizeof(motor.state1.thetawave),
	sizeof(motor.state1.Id_meas),
	sizeof(motor.state1.Iq_meas),
	sizeof(motor.state1.Id_meas_lp),
	sizeof(motor.state1.Iq_meas_lp),
	sizeof(motor.state1.Va),
	sizeof(motor.state1.Vb),
	sizeof(motor.state1.Vc),
	sizeof(motor.state1.VSP),
	sizeof(motor.state1.i_vector_radpers),
	sizeof(motor.state1.i_vector_acc),
	sizeof(motor.state1.Kp_out),
	sizeof(motor.state1.Kp_out_prev),
	sizeof(motor.state1.Kd_out),
	sizeof(motor.state1.Ki_sum),
	sizeof(motor.state1.Ki_out),
	sizeof(motor.state1.lp_out),
	sizeof(motor.state1.biquadout),
	sizeof(motor.state1.mechcontout),
	sizeof(motor.state1.Iout),
	sizeof(motor.state1.muziek_gain),
	sizeof(motor.state1.muziek_gain_V),
	sizeof(motor.state1.downsample),
	sizeof(motor.state1.REFstatus),
	sizeof(motor.state1.incomingByte),
	sizeof(motor.state1.encoderPos1),
	sizeof(motor.state1.encoderPos2),
	sizeof(motor.state1.IndexFound1),
	sizeof(motor.state1.IndexFound2),
	sizeof(motor.state1.OutputOn),
	sizeof(motor.state1.ss_out),
	sizeof(motor.state1.distoff),
	sizeof(motor.state1.dist),
	sizeof(motor.state1.distval),
	sizeof(motor.state1.SP_input_status),
	sizeof(motor.state1.spGO),
	sizeof(motor.state1.Jload),
	sizeof(motor.state1.velFF),
	sizeof(motor.state1.R),
	sizeof(motor.state1.offsetVelTot),
	sizeof(motor.state1.offsetVel),
	sizeof(motor.state1.offsetVel_lp),
	sizeof(motor.state1.offsetVel_lp_prev),
	sizeof(motor.state1.jerk),
	sizeof(motor.state1.acc),
	sizeof(motor.state1.vel),
	sizeof(motor.state1.Ialpha),
	sizeof(motor.state1.Ibeta),
	sizeof(motor.state1.thetaPark),
	sizeof(motor.state1.thetaParkPrev),
	sizeof(motor.state1.edeltarad),
	sizeof(motor.state1.eradpers_lp),
	sizeof(motor.state1.erpm),
	sizeof(motor.state1.thetaPark_enc),
	sizeof(motor.state1.thetaPark_obs),
	sizeof(motor.state1.thetaPark_obs_prev),
	sizeof(motor.state1.co),
	sizeof(motor.state1.si),
	sizeof(motor.state1.tA),
	sizeof(motor.state1.tB),
	sizeof(motor.state1.tC),
	sizeof(motor.state1.Id_e),
	sizeof(motor.state1.Id_SP),
	sizeof(motor.state1.Iq_e),
	sizeof(motor.state1.Iq_SP),
	sizeof(motor.state1.ia),
	sizeof(motor.state1.ib),
	sizeof(motor.state1.ic),
	sizeof(motor.state1.Vq_distgain),
	sizeof(motor.state1.Vd_distgain),
	sizeof(motor.state1.Iq_distgain),
	sizeof(motor.state1.Id_distgain),
	sizeof(motor.state1.mechdistgain),
	sizeof(motor.state1.rdistgain),
	sizeof(motor.state1.maxVolt),
	sizeof(motor.state1.Vtot),
	sizeof(motor.state1.rmech),
	sizeof(motor.state1.rdelay),
	sizeof(motor.state1.emech),
	sizeof(motor.state1.ymech),
	sizeof(motor.state1.rmechoffset),
	sizeof(motor.state1.we),
	sizeof(motor.state1.VqFF),
	sizeof(motor.state1.VdFF),
	sizeof(motor.state1.Iq_offset_SP),
	sizeof(motor.state1.Id_offset_SP),
	sizeof(motor.state1.Valpha_offset),
	sizeof(motor.state1.Vbeta_offset),
	sizeof(motor.state1.vq_int_state),
	sizeof(motor.state1.vd_int_state),
	sizeof(motor.state1.I_bus),
	sizeof(motor.state1.P_tot),
	sizeof(motor.state1.Kp_iq_out),
	sizeof(motor.state1.Ki_iq_out),
	sizeof(motor.state1.Kp_id_out),
	sizeof(motor.state1.Ki_id_out),
	sizeof(motor.state1.Vq_lp_out),
	sizeof(motor.state1.Vd_lp_out),
	sizeof(motor.state1.Vq_biquadout),
	sizeof(motor.state1.Vd_biquadout),
	sizeof(motor.state1.SPdir),
	sizeof(motor.state1.spNgo),
	sizeof(motor.state1.hfi_on),
	sizeof(motor.state1.hfi_V),
	sizeof(motor.state1.hfi_V_act),
	sizeof(motor.state1.hfi_dir),
	sizeof(motor.state1.hfi_dir_int),
	sizeof(motor.state1.hfi_gain),
	sizeof(motor.state1.hfi_curangleest),
	sizeof(motor.state1.hfi_gain_int2),
	sizeof(motor.state1.hfi_Id_meas_low),
	sizeof(motor.state1.hfi_Iq_meas_low),
	sizeof(motor.state1.hfi_Id_meas_high),
	sizeof(motor.state1.hfi_Iq_meas_high),
	sizeof(motor.state1.delta_id),
	sizeof(motor.state1.delta_iq),
	sizeof(motor.state1.hfi_firstcycle),
	sizeof(motor.state1.hfi_abs_pos),
	sizeof(motor.state1.hfi_useforfeedback),
	sizeof(motor.state1.hfi_use_lowpass),
	sizeof(motor.state1.hfi_prev),
	sizeof(motor.state1.hfi_distgain),
	sizeof(motor.state1.hfi_contout),
	sizeof(motor.state1.hfi_error),
	sizeof(motor.state1.hfi_method),
	sizeof(motor.state1.hfi_ffw),
	sizeof(motor.state1.hfi_maxvel),
	sizeof(motor.state1.diq_compensation),
	sizeof(motor.state1.diq_compensation_on),
	sizeof(motor.state1.compensation),
	sizeof(motor.state1.firsterror),
	sizeof(motor.state2.streambuffer),
	sizeof(motor.state2.curbuffer),
	sizeof(motor.state2.buffergain),
	sizeof(motor.state2.runstream),
	sizeof(motor.state2.T_FF_acc),
	sizeof(motor.state2.T_FF_vel),
	sizeof(motor.state2.i_vector_radpers_act),
	sizeof(motor.state2.BEMFa),
	sizeof(motor.state2.BEMFb),
	sizeof(motor.state2.Ialpha_prev),
	sizeof(motor.state2.Ibeta_prev),
	sizeof(motor.state2.Vq),
	sizeof(motor.state2.Vd),
	sizeof(motor.state2.Valpha),
	sizeof(motor.state2.Vbeta),
	sizeof(motor.state2.thetawave),
	sizeof(motor.state2.Id_meas),
	sizeof(motor.state2.Iq_meas),
	sizeof(motor.state2.Id_meas_lp),
	sizeof(motor.state2.Iq_meas_lp),
	sizeof(motor.state2.Va),
	sizeof(motor.state2.Vb),
	sizeof(motor.state2.Vc),
	sizeof(motor.state2.VSP),
	sizeof(motor.state2.i_vector_radpers),
	sizeof(motor.state2.i_vector_acc),
	sizeof(motor.state2.Kp_out),
	sizeof(motor.state2.Kp_out_prev),
	sizeof(motor.state2.Kd_out),
	sizeof(motor.state2.Ki_sum),
	sizeof(motor.state2.Ki_out),
	sizeof(motor.state2.lp_out),
	sizeof(motor.state2.biquadout),
	sizeof(motor.state2.mechcontout),
	sizeof(motor.state2.Iout),
	sizeof(motor.state2.muziek_gain),
	sizeof(motor.state2.muziek_gain_V),
	sizeof(motor.state2.downsample),
	sizeof(motor.state2.REFstatus),
	sizeof(motor.state2.incomingByte),
	sizeof(motor.state2.encoderPos1),
	sizeof(motor.state2.encoderPos2),
	sizeof(motor.state2.IndexFound1),
	sizeof(motor.state2.IndexFound2),
	sizeof(motor.state2.OutputOn),
	sizeof(motor.state2.ss_out),
	sizeof(motor.state2.distoff),
	sizeof(motor.state2.dist),
	sizeof(motor.state2.distval),
	sizeof(motor.state2.SP_input_status),
	sizeof(motor.state2.spGO),
	sizeof(motor.state2.Jload),
	sizeof(motor.state2.velFF),
	sizeof(motor.state2.R),
	sizeof(motor.state2.offsetVelTot),
	sizeof(motor.state2.offsetVel),
	sizeof(motor.state2.offsetVel_lp),
	sizeof(motor.state2.offsetVel_lp_prev),
	sizeof(motor.state2.jerk),
	sizeof(motor.state2.acc),
	sizeof(motor.state2.vel),
	sizeof(motor.state2.Ialpha),
	sizeof(motor.state2.Ibeta),
	sizeof(motor.state2.thetaPark),
	sizeof(motor.state2.thetaParkPrev),
	sizeof(motor.state2.edeltarad),
	sizeof(motor.state2.eradpers_lp),
	sizeof(motor.state2.erpm),
	sizeof(motor.state2.thetaPark_enc),
	sizeof(motor.state2.thetaPark_obs),
	sizeof(motor.state2.thetaPark_obs_prev),
	sizeof(motor.state2.co),
	sizeof(motor.state2.si),
	sizeof(motor.state2.tA),
	sizeof(motor.state2.tB),
	sizeof(motor.state2.tC),
	sizeof(motor.state2.Id_e),
	sizeof(motor.state2.Id_SP),
	sizeof(motor.state2.Iq_e),
	sizeof(motor.state2.Iq_SP),
	sizeof(motor.state2.ia),
	sizeof(motor.state2.ib),
	sizeof(motor.state2.ic),
	sizeof(motor.state2.Vq_distgain),
	sizeof(motor.state2.Vd_distgain),
	sizeof(motor.state2.Iq_distgain),
	sizeof(motor.state2.Id_distgain),
	sizeof(motor.state2.mechdistgain),
	sizeof(motor.state2.rdistgain),
	sizeof(motor.state2.maxVolt),
	sizeof(motor.state2.Vtot),
	sizeof(motor.state2.rmech),
	sizeof(motor.state2.rdelay),
	sizeof(motor.state2.emech),
	sizeof(motor.state2.ymech),
	sizeof(motor.state2.rmechoffset),
	sizeof(motor.state2.we),
	sizeof(motor.state2.VqFF),
	sizeof(motor.state2.VdFF),
	sizeof(motor.state2.Iq_offset_SP),
	sizeof(motor.state2.Id_offset_SP),
	sizeof(motor.state2.Valpha_offset),
	sizeof(motor.state2.Vbeta_offset),
	sizeof(motor.state2.vq_int_state),
	sizeof(motor.state2.vd_int_state),
	sizeof(motor.state2.I_bus),
	sizeof(motor.state2.P_tot),
	sizeof(motor.state2.Kp_iq_out),
	sizeof(motor.state2.Ki_iq_out),
	sizeof(motor.state2.Kp_id_out),
	sizeof(motor.state2.Ki_id_out),
	sizeof(motor.state2.Vq_lp_out),
	sizeof(motor.state2.Vd_lp_out),
	sizeof(motor.state2.Vq_biquadout),
	sizeof(motor.state2.Vd_biquadout),
	sizeof(motor.state2.SPdir),
	sizeof(motor.state2.spNgo),
	sizeof(motor.state2.hfi_on),
	sizeof(motor.state2.hfi_V),
	sizeof(motor.state2.hfi_V_act),
	sizeof(motor.state2.hfi_dir),
	sizeof(motor.state2.hfi_dir_int),
	sizeof(motor.state2.hfi_gain),
	sizeof(motor.state2.hfi_curangleest),
	sizeof(motor.state2.hfi_gain_int2),
	sizeof(motor.state2.hfi_Id_meas_low),
	sizeof(motor.state2.hfi_Iq_meas_low),
	sizeof(motor.state2.hfi_Id_meas_high),
	sizeof(motor.state2.hfi_Iq_meas_high),
	sizeof(motor.state2.delta_id),
	sizeof(motor.state2.delta_iq),
	sizeof(motor.state2.hfi_firstcycle),
	sizeof(motor.state2.hfi_abs_pos),
	sizeof(motor.state2.hfi_useforfeedback),
	sizeof(motor.state2.hfi_use_lowpass),
	sizeof(motor.state2.hfi_prev),
	sizeof(motor.state2.hfi_distgain),
	sizeof(motor.state2.hfi_contout),
	sizeof(motor.state2.hfi_error),
	sizeof(motor.state2.hfi_method),
	sizeof(motor.state2.hfi_ffw),
	sizeof(motor.state2.hfi_maxvel),
	sizeof(motor.state2.diq_compensation),
	sizeof(motor.state2.diq_compensation_on),
	sizeof(motor.state2.compensation),
	sizeof(motor.state2.firsterror),
  }
};

uint8_t signaltomemberlength( uint32_t isignal ) {
  switch ( trace.all_types[isignal] ) {
    case TYPE_INT8:    return(1);
    case TYPE_UINT8:   return(1);
    case TYPE_INT16:   return(2);
    case TYPE_UINT16:  return(2);
    case TYPE_INT32:   return(4);
    case TYPE_UINT32:  return(4);
    case TYPE_INT64:   return(8);
    case TYPE_UINT64:  return(8);
    case TYPE_FLOAT32: return(4);
    case TYPE_FLOAT64: return(8);
    default: return(1);
  }
}
