ElwinBoots/Teensy_DualMotorBoard_V1/Software/stream_object.py

# -*- coding: utf-8 -*-
"""
Created on Sat Oct  7 14:51:16 2023

@author: elwin
"""

Fplayback = m.fs
N_samples_per_write = 100
bufsize = 10000
musicgain1 = 4
musicgain2 = 0

import scipy
import librosa
import os

folder = 'music\\'

#%%
(Fs , data) = scipy.io.wavfile.read( folder + "AC⧸DC - Thunderstruck (Official Video).wav")

stream = data[200*Fs:300*Fs]
stream = scipy.signal.resample(stream , int(len(stream)/Fs*Fplayback) ) 
#%%
(Fs , data) = scipy.io.wavfile.read( folder + "#Stereo： Left and Right Stereo Sound Test.wav")

stream = data[6*Fs:]
stream = scipy.signal.resample(stream , int(len(stream)/Fs*Fplayback) ) 
#%%
(Fs , data) = scipy.io.wavfile.read( folder + "8D Audio Bass Test !!.wav")

stream = data
stream = scipy.signal.resample(stream , int(len(stream)/Fs*Fplayback) ) 
#%%
(Fs , data) = scipy.io.wavfile.read( folder + "Martin Garrix - Animals (Official Video).wav")

stream = data[77*Fs:300*Fs]
stream = scipy.signal.resample(stream , int(len(stream)/Fs*Fplayback) ) 
#%%
(Fs , data) = scipy.io.wavfile.read( folder + "Jedi Mind Tricks Presents： Army Of The Pharaohs - ＂Dump The Clip＂ [Official Audio].wav")

stream = data[8*Fs:]
stream = scipy.signal.resample(stream , int(len(stream)/Fs*Fplayback) ) 
#%%
(Fs , data) = scipy.io.wavfile.read( folder + "Eminem, Dr. Dre - Forgot About Dre (Explicit) (Official Music Video) ft. Hittman.wav")

stream = data
stream = scipy.signal.resample(stream , int(len(stream)/Fs*Fplayback) ) 
#%%
(Fs , data) = scipy.io.wavfile.read( folder + "Lights On ▶ FNAF SECURITY BREACH SONG.wav")

stream = data
stream = scipy.signal.resample(stream , int(len(stream)/Fs*Fplayback) ) 

#%%
(Fs , data) = scipy.io.wavfile.read( folder + "Viva Santa Cruz.wav")

stream = data
stream = scipy.signal.resample(stream , int(len(stream)/Fs*Fplayback) ) 
#%%

fn_mp3 = os.path.join('music', 'It Takes a Seven Nation Army to Hold Us Back (feat. Emilio Lopez).mp3')
stream, Fs = librosa.load(fn_mp3, sr=Fplayback)
# stream = scipy.signal.resample(stream , int(len(stream)/Fs*Fplayback) ) 

#%%
fn_mp3 = os.path.join('music', 'onlymp3.to - Dr Dre - Still D R E ft Snoop Dogg-_CL6n0FJZpk-192k-1688323960.mp3')
stream, Fs = librosa.load(fn_mp3, sr=Fplayback)
stream = stream[int(Fs)*20:]

#%%
fn_mp3 = os.path.join('music', '6 Million Subscribers. Thank you..mp3')
stream, Fs = librosa.load(fn_mp3, sr=Fplayback)

#%%
fn_mp3 = os.path.join('music', 'Hopsin - Kumbaya.mp3')
stream, Fs = librosa.load(fn_mp3, sr=Fplayback)
#%%
fn_mp3 = os.path.join('music', 'Hop Is Back.mp3')
stream, Fs = librosa.load(fn_mp3, sr=Fplayback)
#%%
fn_mp3 = os.path.join('music', 'Eminem - The Real Slim Shady (Official Video - Dirty Version).mp3')
stream, Fs = librosa.load(fn_mp3, sr=Fplayback)

#%%
fn_mp3 = os.path.join('music', 'H.O.P.E. (Hold on Pain Ends).mp3')
stream, Fs = librosa.load(fn_mp3, sr=Fplayback)
#%%
fn_mp3 = os.path.join('music', 'Eminem - Godzilla ft. Juice WRLD (Directed by Cole Bennett).mp3')
stream, Fs = librosa.load(fn_mp3, sr=Fplayback)

#%%
fn_mp3 = os.path.join('music', 'We Live We Love We Lie.mp3')
stream, Fs = librosa.load(fn_mp3, sr=Fplayback)


#%%

if stream.ndim == 1:
  stream = np.tile(stream,(2,1)).T

stream = stream / np.max(np.abs(stream))
L = len(stream)

m.setpar('s1.runstream' , 0)
m.setpar('s1.curbuffer' , 0)
m.setpar('s2.runstream' , 0)
m.setpar('s2.curbuffer' , 0)

for i in range( int(bufsize /N_samples_per_write) ):
   m.setparpart( 's1.streambuffer' ,  stream[ i*N_samples_per_write : (i+1)*N_samples_per_write , 1] , startlocation = np.mod(i*N_samples_per_write , bufsize ) )
   m.setparpart( 's2.streambuffer' ,  stream[ i*N_samples_per_write : (i+1)*N_samples_per_write , 0] , startlocation = np.mod(i*N_samples_per_write , bufsize ) )

m.setpar('s1.runstream' , 1)
m.setpar('s2.runstream' , 1)
m.setpar('s1.buffergain' , musicgain1)
m.setpar('s2.buffergain' , musicgain2)

# m.vel([-20 , 20])
try:
    end = int( (L-bufsize) /N_samples_per_write)
    for i in range( end ):
        # m.CL_cur( i*1900/end+100 , 1)
        # m.CL_cur( i*1900/end+100 , 2)
        # if i == int(end/6):
        #     m.vel([20 , -20])
        # if i == int(end/3):
        #     m.vel([-20 , 20])
        # if i == int(end/2):
        #     m.vel([0 , 0])
        startloc = np.mod(i*N_samples_per_write , bufsize )
        while (startloc  <= m.getsig('s1.curbuffer') <= startloc + N_samples_per_write):
            pass
        m.setparpart( 's1.streambuffer' ,  stream[ i*N_samples_per_write + bufsize: (i+1)*N_samples_per_write + bufsize , 1] , startlocation = startloc )
        m.setparpart( 's2.streambuffer' ,  stream[ i*N_samples_per_write + bufsize: (i+1)*N_samples_per_write + bufsize , 0] , startlocation = startloc )
        # print((i+1)*N_samples_per_write + bufsize)z
except:
    time.sleep(0.1)   
    m.ser.flushInput()  
    print('Canceled')
  
m.setpar('s1.buffergain' , 0)
m.setpar('s2.buffergain' , 0)
m.setpar('s1.runstream' , 0)
m.setpar('s2.runstream' , 0)
